csmarshall/fridge-display-mount/strut/clamp_sheets.py

#!/usr/bin/env python3
"""The clamped-strut design's drawing set.

Every sheet reads the SAME `Assembly` the concept sheet does, so a dimension cannot be right on
one drawing and stale on another. Nothing here is measured off a picture; if a number appears, it
was derived from `Assembly` or it is flagged as an estimate.

Sheets:
  clamp_approval      partner-facing: what it is, what it costs, what it looks like
  clamp_parts         flat patterns for the two bent parts, with bend lines and the deduction
  clamp_assembly      the order it goes together, and what is loose at each step
  clamp_clearance     plan view: where the top clamp lands in the 406 mm hinge window
  clamp_loadpath      where the weight actually goes
  clamp_height_check  does a strut slot land where each clamp needs one
"""
from __future__ import annotations

import argparse
import logging
import math
import sys
from pathlib import Path
from typing import Sequence

from concept_sheet import (IN, INK, MUTED, RULE, PAPER, OK, BAD, WARN,
                           C_STEEL, C_STRUT, C_PLATE, Assembly, _t, _wrap)

LOG = logging.getLogger("clamp")

FRIDGE_SIDE, FRIDGE_EDGE = "#3a3734", "#2b2926"
PAD_FILL, PAD_EDGE = "#f8e2a4", "#c9a227"
BAND = "#b8860b"


def _frame(w, h, title, sub, banner) -> list[str]:
    return [f'<svg xmlns="http://www.w3.org/2000/svg" width="{w:.0f}" height="{h:.0f}" '
            f'viewBox="0 0 {w:.0f} {h:.0f}">',
            f'<rect width="{w:.0f}" height="{h:.0f}" fill="{PAPER}"/>',
            f'<rect width="{w:.0f}" height="24" fill="{BAND}"/>',
            _t(w / 2, 16.5, banner, 11.5, fill="#fff", weight="bold"),
            _t(40, 56, title, 21, anchor="start", weight="bold"),
            _t(40, 78, sub, 12.5, anchor="start", fill=MUTED)]


def _panel(x, y, w, h, title, colour=INK) -> list[str]:
    return [f'<rect x="{x:.1f}" y="{y:.1f}" width="{w:.1f}" height="{h:.1f}" rx="7" fill="#fff" '
            f'stroke="{RULE}" stroke-width="1"/>',
            _t(x + 16, y + 24, title, 12.5, anchor="start", weight="bold", fill=colour)]


def _para(x, y, text, limit=74, size=10.6, lead=13.0, fill=MUTED) -> list[str]:
    return [_t(x, y + i * lead, ln, size, anchor="start", fill=fill)
            for i, ln in enumerate(_wrap(text, limit))]


def _display_ghost(x, y, w, h, label="23.8 in display — TRUE SCALE") -> list[str]:
    """The one object whose size the reader already knows. Dashed, never filled solid."""
    return [f'<rect x="{x:.1f}" y="{y:.1f}" width="{w:.1f}" height="{h:.1f}" fill="#101820" '
            f'fill-opacity="0.10" stroke="{INK}" stroke-width="1.4" stroke-dasharray="7 4"/>',
            _t(x + w / 2, y + h / 2, label, 9.0, fill=MUTED, weight="bold")]


def bend_deduction(a: Assembly) -> float:
    """SendCutSend's PUBLISHED deduction for this gauge. One home: Assembly.bend_deduction."""
    return a.bend_deduction


def slot_centres(a: Assembly) -> list[float]:
    """Strut slot centres above the strut's own bottom end."""
    n = int((a.strut_len - 25.4) / a.slot_pitch) + 1
    return [25.4 + i * a.slot_pitch for i in range(n)]


def nearest_slot(a: Assembly, want: float) -> tuple[float, float]:
    """(centre, signed offset) of the slot nearest a wanted height."""
    c = min(slot_centres(a), key=lambda s: abs(s - want))
    return c, c - want


# --------------------------------------------------------------------------------------------
def sheet_parts(path: Path, a: Assembly) -> None:
    """Flat patterns. Formed dimensions in, flat length derived by subtracting the deduction."""
    W, H = 1180, 760
    bd = bend_deduction(a)
    o = _frame(W, H, "THE TWO PARTS, FLAT",
               f"Two bent parts: {a.n_clamps} clamps and {a.n_feet} feet. TWO surfaces are "
               f"gripped (the fridge top and its underside) but the clamps SPAN both struts, so "
               f"that is {a.n_clamps} bars, not {a.n_struts * a.clamped_surfaces} tabs.",
               "FLAT PATTERNS — dimensions derived, bend deduction is an ESTIMATE until "
               "SendCutSend's calculator confirms it")

    half = a.strut_spacing / 2.0
    PARTS = [(f"A — CLAMP BAR  x{a.n_clamps}", a.clamp_leg, a.clamp_short, a.clamp_width,
              [-half, half], "round",
              "Spans BOTH struts, so the two legs are tied into a frame rather than standing "
              "independently. Long leg lies on the fridge top, or under its base. The SAME part "
              "does both ends — the lower one is flipped."),
             (f"B — FOOT  x{a.n_feet}", a.foot_leg, a.foot_rise, a.foot_width,
              [0.0], "slot",
              "One per strut. Vertical leg carries the elongated slot the stud passes through; "
              "horizontal leg turns OUTBOARD and the strut stands on it, so the strut never "
              "touches the floor.")]

    # ONE scale for both parts, fitted to whichever dimension binds. The clamp is now 5.5x the
    # foot's width, so scaling each to its own panel would make them impossible to compare.
    sc = min(390.0 / max(lg + sh - bd for _, lg, sh, _, _, _, _ in PARTS),
             186.0 / max(wd for _, _, _, wd, _, _, _ in PARTS))

    for idx, (nm, leg, short, wid, holes, hkind, note) in enumerate(PARTS):
        px, py = 40 + idx * 580, 100
        o += _panel(px, py, 545, 470, nm, OK)
        flat_len = leg + short - bd
        fw = wid * sc
        bx = px + 40
        by = py + 142 + (186.0 - fw) / 2.0
        o.append(f'<rect x="{bx:.1f}" y="{by:.1f}" width="{flat_len * sc:.1f}" '
                 f'height="{fw:.1f}" fill="{C_PLATE}" stroke="{INK}" stroke-width="1.4"/>')
        blx = bx + (leg - bd / 2.0) * sc
        o.append(f'<line x1="{blx:.1f}" y1="{by - 14:.1f}" x2="{blx:.1f}" '
                 f'y2="{by + fw + 14:.1f}" stroke="{BAD}" stroke-width="1.5" '
                 f'stroke-dasharray="8 5"/>')
        o.append(_t(blx, by - 20, "BEND 90", 9.0, fill=BAD, weight="bold"))

        hx = bx + (leg * 0.55) * sc
        for hy_mm in holes:
            cy = by + fw / 2.0 + hy_mm * sc
            if hkind == "round":
                o.append(f'<circle cx="{hx:.1f}" cy="{cy:.1f}" r="{a.bolt_dia * sc / 2:.1f}" '
                         f'fill="{PAPER}" stroke="{INK}" stroke-width="1.1"/>')
            else:
                sl = a.slot_len * sc
                o.append(f'<rect x="{hx - sl / 2:.1f}" y="{cy - 4:.1f}" width="{sl:.1f}" '
                         f'height="8" rx="4" fill="{PAPER}" stroke="{INK}" stroke-width="1.1"/>')
        if hkind == "round":
            o.append(f'<line x1="{hx:.1f}" y1="{by + fw / 2 - half * sc:.1f}" x2="{hx:.1f}" '
                     f'y2="{by + fw / 2 + half * sc:.1f}" stroke="{OK}" stroke-width="1"/>')
            lx = bx + flat_len * sc + 12
            o.append(f'<line x1="{hx:.1f}" y1="{by + fw / 2:.1f}" x2="{lx - 4:.1f}" '
                     f'y2="{by + fw / 2:.1f}" stroke="{OK}" stroke-width="0.7" '
                     f'stroke-dasharray="3 3"/>')
            o.append(_t(lx, by + fw / 2 - 3, f"{a.strut_spacing:.0f} mm", 9.4, anchor="start",
                        fill=OK, weight="bold"))
            o.append(_t(lx, by + fw / 2 + 9, "strut centres", 8.6, anchor="start", fill=OK))
            o.append(_t(bx + flat_len * sc / 2, by + fw + 24,
                        "square holes 8.38 — the stud cannot spin", 8.6, fill=MUTED))
        else:
            o.append(_t(bx + flat_len * sc / 2, by + fw + 24,
                        f"slot {a.slot_len:.1f} long — height adjustment lives HERE", 8.6,
                        fill=MUTED))

        dy = by + fw + 48
        for x0, x1, txt in [(bx, blx, f"{leg:.0f} formed"),
                            (blx, bx + flat_len * sc, f"{short:.0f} formed")]:
            o.append(f'<line x1="{x0:.1f}" y1="{dy:.1f}" x2="{x1:.1f}" y2="{dy:.1f}" '
                     f'stroke="{INK}" stroke-width="0.8"/>')
            o.append(_t((x0 + x1) / 2, dy - 5, txt, 9.0, weight="bold"))
        o.append(_t(bx + flat_len * sc / 2, dy + 26,
                    f"FLAT {flat_len:.2f} x {wid:.0f}", 10.5, weight="bold"))
        o += _para(px + 16, py + 54, note, 62)
        o += _para(px + 16, py + 424,
                   f"Material {a.bracket_t:.2f} mm ({a.bracket_t / IN:.3f} in), bend radius "
                   f"{a.bend_radius:.2f} (SendCutSend published), deduction {bd:.2f} mm (published). "
                   f"Both parts drawn at the SAME scale.", 62)

    o += _panel(40, 590, 1085, 130, "WHAT SPANNING COSTS, AND THE ONE RISK IT CARRIES", WARN)
    o += _para(56, 636,
               f"Two bars instead of four tabs uses about 2.7x the clamp steel, and the top bar "
               f"now fixes the {a.strut_spacing:.0f} mm spacing instead of relying on careful "
               f"assembly — which is a gain. The risk is underneath: the LOWER bar has to bear "
               f"across {a.clamp_width:.0f} mm of an underside measured at 10-20 mm and known "
               f"NOT to be flat. It therefore bears on TWO PADS inset {a.lower_pad_inset:.0f} mm "
               f"from each strut rather than along a continuous edge, so an uneven surface loads "
               f"two known points instead of whichever high spot it finds first.", 150)
    o.append("</svg>")
    path.write_text("".join(o), encoding="utf-8")
    LOG.info("Wrote %s — %d clamps x %.0f mm span, %d feet, deduction %.2f",
             path, a.n_clamps, a.clamp_width, a.n_feet, bd)


# --------------------------------------------------------------------------------------------
def sheet_height_check(path: Path, a: Assembly) -> None:
    """Does a slot actually land where each clamp needs one? Asked for explicitly."""
    W, H = 1180, 720
    top_c, top_off = nearest_slot(a, a.fridge_h)
    low_c, low_off = nearest_slot(a, a.base_gap)
    reach = a.slot_len / 2.0
    o = _frame(W, H, "DOES A SLOT LAND WHERE EACH CLAMP NEEDS ONE?",
               "The strut is slotted on a fixed 50.8 mm pitch. The fridge is whatever height it "
               "is. Those two facts have to meet.",
               "VALIDATION — the check that the strut can actually be bolted where it must be")

    o += _panel(40, 100, 700, 470, "STRUT SLOTS vs THE TWO CLAMP HEIGHTS")
    ox, oy, sc = 250.0, 552.0, 0.212
    def Y(mm):
        return oy - mm * sc
    pieces = ([(0.0, a.lower_strut_len), (a.upper_strut_lo, a.strut_top)] if a.strut_split
              else [(0.0, a.strut_len)])
    for p_lo, p_hi in pieces:
        o.append(f'<rect x="{ox:.1f}" y="{Y(p_hi):.1f}" width="26" '
                 f'height="{(Y(p_lo) - Y(p_hi)):.1f}" fill="{C_STRUT}" stroke="{INK}" '
                 f'stroke-width="1.1"/>')
        for s in a._slots_between(p_lo, p_hi - 11.11, p_lo):
            o.append(f'<rect x="{ox + 8:.1f}" y="{Y(s + a.slot_len / 2):.1f}" width="10" '
                     f'height="{a.slot_len * sc:.1f}" fill="{INK}" fill-opacity="0.45"/>')
    if a.strut_split:
        o.append(f'<rect x="{ox - 3:.1f}" y="{Y(a.upper_strut_lo):.1f}" width="32" '
                 f'height="{(Y(a.lower_strut_len) - Y(a.upper_strut_lo)):.1f}" fill="{OK}" '
                 f'fill-opacity="0.14"/>')
        o.append(_t(ox + 13, (Y(a.lower_strut_len) + Y(a.upper_strut_lo)) / 2, "GAP", 8.0,
                    fill=OK, weight="bold"))
    o.append(f'<line x1="{ox - 150:.1f}" y1="{Y(a.fridge_h):.1f}" x2="{ox + 150:.1f}" '
             f'y2="{Y(a.fridge_h):.1f}" stroke="{FRIDGE_EDGE}" stroke-width="1.2"/>')
    o.append(f'<rect x="{ox - 150:.1f}" y="{Y(a.fridge_h):.1f}" width="150" '
             f'height="{(Y(a.base_gap) - Y(a.fridge_h)):.1f}" fill="{FRIDGE_SIDE}"/>')
    o.append(_t(ox - 75, Y(a.fridge_h / 2), "fridge", 9, fill="#cfc9c2", rot=-90))

    rowspec = [(a.fridge_h, "TOP CLAMP", a.upper_strut_lo),
               (a.base_gap, "LOWER CLAMP", 0.0),
               (a.plate_bolt_hi, "PLATE, upper bolts", a.upper_strut_lo),
               (a.plate_bolt_lo, "PLATE, lower bolts", 0.0)] if a.strut_split else [
               (a.fridge_h, "TOP CLAMP", 0.0), (a.base_gap, "LOWER CLAMP", 0.0)]
    packed = []
    for want, nm, origin in rowspec:
        cand = a._slots_between(origin, origin + 4000, origin)
        cen = min(cand, key=lambda s: abs(s - want))
        packed.append((want, cen, cen - want, nm))
    for want, cen, off, nm in packed:
        ok = abs(off) <= reach
        col = OK if ok else BAD
        o.append(f'<line x1="{ox + 26:.1f}" y1="{Y(want):.1f}" x2="{ox + 170:.1f}" '
                 f'y2="{Y(want):.1f}" stroke="{col}" stroke-width="1.5"/>')
        o.append(_t(ox + 176, Y(want) - 12, f"{nm} wants {want:.1f}", 9.5, anchor="start",
                    fill=col, weight="bold"))
        o.append(_t(ox + 176, Y(want) + 1, f"nearest slot {cen:.1f}, off by {off:+.1f}", 8.6,
                    anchor="start", fill=col))
        o.append(_t(ox + 176, Y(want) + 13,
                    f"{'INSIDE' if ok else 'OUTSIDE'} the {reach:.1f} half-slot", 8.6,
                    anchor="start", fill=col, weight="bold"))

    o.append(f'<line x1="{ox + 13:.1f}" y1="{Y(a.strut_len):.1f}" x2="{ox + 13:.1f}" '
             f'y2="{Y(a.fridge_h):.1f}" stroke="{WARN}" stroke-width="2"/>')
    o.append(_t(ox + 40, Y(a.fridge_h) - 14, f"{a.proud:.1f} mm proud of the top", 9.0,
                anchor="start", fill=WARN, weight="bold"))

    o += _panel(760, 100, 380, 470, "WHAT THE NUMBERS SAY", OK)
    rows = [("strut, lower + upper", f"{a.lower_strut_ft:.0f}+{a.upper_strut_ft:.0f} ft",
             "both stock, no cutting"),
            ("fridge case height", f"{a.fridge_h:.1f}", "published"),
            ("strut stands proud by", f"{a.proud:.1f}", "derived"),
            ("slot pitch", f"{a.slot_pitch:.1f}", "McMaster table"),
            ("slot length", f"{a.slot_len:.1f}", "McMaster table"),
            ("adjustment either way", f"±{reach:.1f}", "half a slot"),
            ("lower piece", f"{a.lower_strut_ft:.0f} ft", "stock, no cut"),
            ("upper piece", f"{a.upper_strut_ft:.0f} ft", "stock, no cut"),
            ("gap over the box", f"{a.upper_strut_lo - a.lower_strut_len:.1f}",
             f"{a.edge_open:.0f} of {a.box_h_portrait:.0f} mm edge open")] + [
            (nm.lower(), f"{off:+.1f}", "PASS" if abs(off) <= reach else "FAIL")
            for _, _, off, nm in packed]
    for i, (k, v, n) in enumerate(rows):
        ry = 140 + i * 34
        if i % 2 == 0:
            o.append(f'<rect x="770" y="{ry - 15:.1f}" width="360" height="30" fill="#f2f5f7"/>')
        col = OK if n == "PASS" else (BAD if n == "FAIL" else MUTED)
        o.append(_t(782, ry + 2, k, 10.4, anchor="start"))
        o.append(_t(1035, ry + 2, v, 10.8, anchor="end", weight="bold"))
        o.append(_t(1048, ry + 2, n, 9.2, anchor="start", fill=col,
                    weight="bold" if col is not MUTED else "normal"))

    o += _panel(40, 590, 1100, 110, "THE POINT", OK if abs(top_off) <= reach else BAD)
    o += _para(56, 640,
               f"Four landings on TWO slot grids, because each piece anchors its own slots to its "
               f"own end. Three are EXACT and one is {max(abs(o_) for _, _, o_, _ in packed):.1f} "
               f"mm out, all inside the {reach:.1f} mm half-slot. The exact ones are not luck: "
               f"strut_top_proud is DERIVED to put a slot on the top clamp — at an arbitrary "
               f"60 mm the nearest was 16.2 mm away, outside the half-slot and unbuildable. The "
               f"plate bolts are exact by construction, because they are CHOSEN from real slot "
               f"positions rather than picked and hoped for.", 152)
    o.append("</svg>")
    path.write_text("".join(o), encoding="utf-8")
    worst = max(abs(off) for _, _, off, _ in packed)
    LOG.info("Wrote %s — %d landings checked on %d slot grids, worst %+.2f against ±%.1f", path, len(packed), 2 if a.strut_split else 1, worst, reach)


# --------------------------------------------------------------------------------------------
def sheet_loadpath(path: Path, a: Assembly) -> None:
    W, H = 1180, 700
    o = _frame(W, H, "WHERE THE WEIGHT ACTUALLY GOES",
               "Straight down the strut, into the foot, into the floor. The clamps do not carry "
               "it — they only stop the top falling away from the wall.",
               "LOAD PATH — the whole argument for this design in one drawing")
    ox, oy, sc = 250.0, 590.0, 0.255
    def Y(mm):
        return oy - mm * sc
    o += _panel(40, 100, 700, 500, "SIDE VIEW, TO SCALE")
    o.append(f'<rect x="{ox:.1f}" y="{Y(a.fridge_h):.1f}" width="{160 * sc * 2:.1f}" '
             f'height="{(Y(a.base_gap) - Y(a.fridge_h)):.1f}" fill="{FRIDGE_SIDE}"/>')
    sx = ox + 160 * sc * 2 + 10
    o.append(f'<rect x="{sx:.1f}" y="{Y(a.strut_len):.1f}" width="14" '
             f'height="{a.strut_len * sc:.1f}" fill="{C_STRUT}" stroke="{INK}"/>')
    o.append(f'<line x1="{ox - 90:.1f}" y1="{oy:.1f}" x2="{sx + 190:.1f}" y2="{oy:.1f}" '
             f'stroke="{INK}" stroke-width="2.5"/>')
    o += _display_ghost(sx + 46, Y(a.screen_centre + a.display_h / 2), 26,
                        a.display_h * sc, "display")
    for yy in range(0, 5):
        ay = Y(a.screen_centre) + yy * 60
        if ay > oy - 20:
            break
        o.append(f'<line x1="{sx + 7:.1f}" y1="{ay:.1f}" x2="{sx + 7:.1f}" y2="{ay + 44:.1f}" '
                 f'stroke="{OK}" stroke-width="3"/>')
        o.append(f'<path d="M{sx + 2:.1f} {ay + 38:.1f} L{sx + 7:.1f} {ay + 48:.1f} '
                 f'L{sx + 12:.1f} {ay + 38:.1f}" fill="{OK}"/>')
    o.append(_t(sx + 60, Y(700), "the load runs DOWN the strut", 10.5, anchor="start", fill=OK,
                weight="bold"))
    o.append(_t(sx + 60, Y(660), "and into the floor, not the fridge", 10.0, anchor="start",
                fill=OK))
    for h, nm in [(a.fridge_h, "top clamp — HOLDS IN, carries nothing"),
                  (a.base_gap, "lower clamp — HOLDS IN, carries nothing")]:
        o.append(f'<path d="M{sx - 30:.1f} {Y(h):.1f} L{sx - 4:.1f} {Y(h):.1f}" stroke="{WARN}" '
                 f'stroke-width="2.5"/>')
        o.append(f'<path d="M{sx - 10:.1f} {Y(h) - 5:.1f} L{sx - 2:.1f} {Y(h):.1f} '
                 f'L{sx - 10:.1f} {Y(h) + 5:.1f}" fill="{WARN}"/>')
        o.append(_t(sx + 22, Y(h) - 8, nm, 9.2, anchor="start", fill=WARN, weight="bold"))
    o.append(f'<rect x="{sx - 6:.1f}" y="{oy - 7:.1f}" width="74" height="7" fill="{C_STEEL}" '
             f'stroke="{INK}" stroke-width="0.9"/>')
    o.append(_t(sx + 74, oy - 12, "FOOT", 9.0, anchor="start", fill=OK, weight="bold"))
    o.append(_t(ox + 60, oy - 18, "FLOOR — takes all 154 N", 10.5, anchor="start",
                weight="bold"))

    o += _panel(760, 100, 380, 500, "WHAT THAT BUYS", OK)
    pts = [("No magnets at all", "the derate chain, the fastener stack, the peel failure mode "
            "and the dependency on a magnetic panel all vanish together."),
           ("A non-magnetic panel stops mattering", "stainless, plastic, painted — the clamp "
            "does not care what the fridge is made of."),
           ("Nothing creeps", "sustained shear on paint was the slow failure the magnets had. "
            "There is no sustained shear here."),
           ("Height became adjustable", "the foot's slot sets it, after the thing is built, "
            "against a real person standing there."),
           ("The failure mode changed", "the magnet design's worst case was bonded glass on the "
            "floor. This one's is a wobble.")]
    for i, (hd, bd_) in enumerate(pts):
        yy = 146 + i * 92
        o.append(_t(776, yy, hd, 11.0, anchor="start", weight="bold", fill=OK))
        o += _para(776, yy + 17, bd_, 44, size=10.0, lead=12.5)
    o.append("</svg>")
    path.write_text("".join(o), encoding="utf-8")
    LOG.info("Wrote %s", path)


# --------------------------------------------------------------------------------------------
def sheet_clearance(path: Path, a: Assembly) -> None:
    W, H = 1180, 640
    o = _frame(W, H, "WHERE THE TOP CLAMP LANDS",
               "Plan view of the fridge top. The hinge cover owns the front; the clamp has to "
               "live behind it.",
               "CLEARANCE — the window is derived and the tape agrees; the LAYOUT inside it is the finding")
    ox, oy, sc = 90.0, 150.0, 1.05
    o += _panel(40, 100, 1100, 330, "FRIDGE TOP, LOOKING DOWN")
    o.append(f'<rect x="{ox:.1f}" y="{oy:.1f}" width="{a.fridge_d * sc:.1f}" height="150" '
             f'fill="{FRIDGE_SIDE}" stroke="{FRIDGE_EDGE}"/>')
    hc_x = ox + (a.fridge_d - a.hinge_cover) * sc
    o.append(f'<rect x="{hc_x:.1f}" y="{oy:.1f}" width="{a.hinge_cover * sc:.1f}" height="150" '
             f'fill="#5c574f" stroke="{FRIDGE_EDGE}"/>')
    o.append(_t(hc_x + a.hinge_cover * sc / 2, oy + 78, "HINGE COVER", 10.5, fill="#e8e2d8",
                weight="bold"))
    o.append(_t(hc_x + a.hinge_cover * sc / 2, oy + 94, f"front {a.hinge_cover:.0f} mm", 9,
                fill="#bdb6ab"))
    o.append(_t(ox + 40, oy + 20, "REAR", 9, anchor="start", fill="#bdb6ab"))

    centre = a.strut_centre          # the WINDOW's centre, not the case's — see Assembly
    for s in (centre - a.strut_spacing / 2.0, centre + a.strut_spacing / 2.0):
        cx = ox + s * sc
        o.append(f'<rect x="{cx - a.strut_width * sc / 2:.1f}" y="{oy + 30:.1f}" '
                 f'width="{a.strut_width * sc:.1f}" height="90" fill="{C_STRUT}" '
                 f'stroke="{INK}" stroke-width="1.2"/>')

    margin = a.hinge_margin
    bar_x = ox + (centre - a.clamp_outer_half) * sc
    o.append(f'<rect x="{bar_x:.1f}" y="{oy + 40:.1f}" width="{a.clamp_width * sc:.1f}" '
             f'height="70" fill="{C_STEEL}" fill-opacity="0.9" stroke="{INK}" '
             f'stroke-width="1.3"/>')
    o.append(_t(ox + centre * sc, oy + 72,
                f"ONE CLAMP BAR spanning both struts — {a.clamp_width:.0f} mm", 9.4, fill="#fff",
                weight="bold"))
    o.append(_t(ox + centre * sc, oy + 88, "ties the two struts into a frame", 8.4,
                fill="#d8d2c8"))
    front_edge = centre + a.clamp_outer_half
    o.append(f'<line x1="{ox + front_edge * sc:.1f}" y1="{oy + 160:.1f}" x2="{hc_x:.1f}" '
             f'y2="{oy + 160:.1f}" stroke="{BAD if margin < 10 else OK}" stroke-width="1.6"/>')
    o.append(_t((ox + front_edge * sc + hc_x) / 2, oy + 145, f"{margin:.1f} mm", 10,
                fill=BAD if margin < 10 else OK, weight="bold"))
    o.append(f'<line x1="{ox:.1f}" y1="{oy + 200:.1f}" x2="{hc_x:.1f}" y2="{oy + 200:.1f}" '
             f'stroke="{INK}" stroke-width="1"/>')
    o.append(_t((ox + hc_x) / 2, oy + 194, f"clear window {a.clear_window:.1f} mm — derived; the 406 tape reading agrees",
                10, weight="bold"))

    o += _panel(40, 450, 1100, 160, "READ THIS THE RIGHT WAY ROUND", WARN)
    o += _para(56, 500,
               f"The bar is placed as far FORWARD as the cover allows while holding "
               f"{a.cover_margin:.0f} mm back from it, which leaves {a.strut_centre - a.clamp_outer_half:.1f} mm "
               f"at the rear. Three datums were possible. Centring on the CASE drives the bar "
               f"48.7 mm INTO the cover — blocked. Centring on the WINDOW is safe but leaves the "
               f"screen 101.5 mm behind the case centre, pushed away from where anyone stands. "
               f"Going hard forward centres best and leaves ZERO tolerance against a cover "
               f"position read off a photograph. This sits between them: the screen is now "
               f"{a.display_bias_rearward:.1f} mm rearward instead of 101.5, and "
               f"{a.cover_margin:.0f} mm of clearance is deliberately kept in hand.", 150)
    o.append("</svg>")
    path.write_text("".join(o), encoding="utf-8")
    LOG.info("Wrote %s — installed margin %.1f mm", path, margin)


# --------------------------------------------------------------------------------------------
def sheet_assembly(path: Path, a: Assembly) -> None:
    W, H = 1180, 700
    o = _frame(W, H, "HOW IT GOES TOGETHER",
               "Four steps. Everything stays loose until the last one, because the fridge is what "
               "squares it up.",
               "ASSEMBLY — order matters; tightening early is the way to get this wrong")
    steps = [("1  STAND THE STRUTS ON THE FEET",
              "Stud through the foot's slot and the strut's bottom slot. Nut FINGER TIGHT. The "
              "slot is the height adjustment, so leaving it loose is the whole point.",
              "loose"),
             ("2  HOOK THE TOP CLAMP BAR OVER",
              "ONE bar across both struts. Long leg on the fridge top, short leg down beside "
              "them, washers behind. Nuts on, still loose. Because it reaches both struts it "
              "SETS the spacing for you rather than needing it measured.",
              "loose"),
             ("3  SLIDE THE LOWER BAR UP",
              "Up until its two pads engage under the appliance. Pads, not a continuous edge, "
              "because the underside is not flat. This is the step that needs a torch and the "
              "one with an open question against it.",
              "loose"),
             ("4  PLATE ON, THEN THE DISPLAY — IN THAT ORDER",
              "The plate-to-strut bolt heads sit on the display side. Once the display is "
              "mounted they cannot be reached, so the plate goes on first and the display last.",
              "TIGHT"),
             ("5  LOCK EVERYTHING",
              "Top first, then bottom, then the feet. The struts go into tension between the two "
              "clamps and the fridge is gripped rather than leaned on.",
              "TIGHT")]
    for i, (hd, body, state) in enumerate(steps):
        x = 40 + (i % 2) * 570
        y = 100 + (i // 2) * 210
        col = OK if state == "TIGHT" else WARN
        o += _panel(x, y, 540, 185, hd, col)
        o += _para(x + 16, y + 50, body, 62)
        o.append(f'<rect x="{x + 16:.1f}" y="{y + 140:.1f}" width="{62 + len(state) * 6:.0f}" '
                 f'height="22" rx="11" fill="{col}" fill-opacity="0.14"/>')
        o.append(_t(x + 26, y + 155, f"leave it {state}", 9.6, anchor="start", fill=col,
                    weight="bold"))
    o += _panel(40, 530, 1100, 140, "THE ONE THING THAT WILL BITE", BAD)
    o += _para(56, 580,
               f"Tightening the top bar before the lower one is engaged pulls the struts "
               f"against the panel at an angle and they will not then slide. The struts are "
               f"{a.strut_len:.0f} mm of stiff channel; there is no compliance in them to take "
               f"that out afterwards. If a lower clamp will not move, slacken the top and start "
               f"again rather than forcing it. Only the {a.foam:.0f} mm foam has any give at all, "
               f"and it has {a.foam:.0f} mm of it.", 150)
    o.append("</svg>")
    path.write_text("".join(o), encoding="utf-8")
    LOG.info("Wrote %s", path)
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
