csmarshall/fridge-display-mount/plate_fea.py

#!/usr/bin/env python3
"""Plate finite-element check of the BODY plate, with its real holes, under a touch press.

The generators size the plate with a strip-beam model: a magnet-disc-wide strip cantilevered
from the VESA screw, which is easy, conservative and cannot see the holes. This replaces it
with a Kirchhoff plate solved by finite elements (Morley element, scikit-fem) on a gmsh mesh
of the plate exactly as cut: outline fillets, centre vent, four windows, every hole.

Load case — the governing one from CLAUDE.md 1.2: a 5 lb press at the outer screen edge is a
torsion M = F x torsion_arm about the plate normal through the VESA centre. The display box
delivers it to the plate as a COUPLE at the four VESA screws: +F/2 on the two screws of one
column, -F/2 on the other, F = M / vesa. Everything that holds the plate to the panel is
modelled as PINNED over its footprint:

    magnets   the four fitted magnet discs (phase 1 of the third design; the archived hook)
    struts    the elevator-bolt head footprint at each strut bolt (phase 2)

Reported: plate deflection at each VESA screw, the rotation of the VESA pattern, and the
screen-edge movement that rotation implies (rotation x torsion_arm) — the number the strip
model calls "screen edge", so the two can be compared directly.

What this is NOT: a stress check (the strip SF numbers stand, and are large), a model of the
neck or arm (the body is cut free at the neck junction, which is conservative), or a contact
model of the magnets (pinned, not bonded — no uplift allowed, which is the optimistic side).
Treat the results as "the plate answer", not "the truth".

Reads a params JSON written by generate_bracket.py, so the plate here IS the plate cut.
"""
from __future__ import annotations

import argparse
import json
import logging
import math
import sys
from dataclasses import dataclass
from pathlib import Path
from typing import Sequence

import numpy as np

from bracket_common import LOG_LEVELS, configure_logging

LOG = logging.getLogger("fea")

E_STEEL_MPA = 200_000.0
NU_STEEL = 0.29
N_PER_LBF = 4.4482216
ELEVATOR_HEAD_DIA = (1 + 3 / 16) * 25.4     # McMaster 92670A781 head, the strut-side footprint


@dataclass(frozen=True)
class Case:
    support: str           # "magnets" | "struts"
    thickness_mm: float
    w_screws: tuple[float, ...]   # deflection at the 4 VESA screws, mm (+ toward the panel)
    w_max: float
    rotation_rad: float
    screen_edge_mm: float
    n_elements: int
    support_desc: str
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
